greengravity/Datakey/core/coreprocessor.X/assets/assets.c

#include "assets.h"

// Systemfont: 16 pixels high
const uint16_t bitmapdata[] = 
{
// @0" " (3 pixels wide)
//    
//    
//    
//    
//    
//    
//    
//    
//    
//    
//    
//    
//    
//    
//    
//    
0x0000,0x0000,0x0000,0x0000,0x0000,0x0000,0x0000,0x0000,0x0000,0x0000,0x0000,0x0000,0x0000,0x0000,0x0000,0x0000,0x0000,0x0000,0x0000,0x0000,0x0000,0x0000,0x0000,0x0000,0x0000,0x0000,0x0000,0x0000,0x0000,0x0000,0x0000,0x0000,0x0000,0x0000,0x0000,0x0000,0x0000,0x0000,0x0000,0x0000,0x0000,0x0000,0x0000,0x0000,0x0000,0x0000,0x0000,0x0000
// @48"!" (3 pixels wide)
//    
//    
//    
//    
//  # 
//  # 
//  # 
//  # 
//  # 
//  # 
//    
//  # 
//  # 
//    
//    
//    
,0x0000,0x0000,0x0000,0x0000,0x0000,0x0000,0x0000,0x0000,0x0000,0x0000,0x0000,0x0000,0x4208,0xe73c,0x4208,0x4208,0xe73c,0x4208,0x4208,0xe73c,0x4208,0x4208,0xe73c,0x4208,0x2104,0xdedb,0x4208,0x2104,0xce79,0x2104,0x0000,0x0000,0x0000,0x4208,0xe73c,0x4208,0x4208,0xe73c,0x4208,0x0000,0x0000,0x0000,0x0000,0x0000,0x0000,0x0000,0x0000,0x0000
// @96""" (5 pixels wide)
//      
//      
//      
//  # # 
//  # # 
//  # # 
//  # # 
//      
//      
//      
//      
//      
//      
//      
//      
//      
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
  { 90,0, 7, 122 }, // z
  { 91,0, 6, 123 }, // {
  { 92,2, 6, 124 }, // |
  { 93,0, 7, 125 }, // }
  { 94,0, 9, 126 }, // ~
  { 95,0, 7, 167 }, // §
  { 96,0, 6, 176 }, // °
  { 97,0, 6, 178 }, // ²
  { 98,0, 6, 179 }, // ³
  { 99,2, 7, 180 }, // ´
  { 100,0, 10, 196 }, // Ä
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
};

const Unicodelist unicodes[] = 
{
  { 0,0 }, // zero
  { 32,1 }, //  
  { 33,2 }, // !
  { 34,3 }, // "
  { 35,4 }, // #
  { 36,5 }, // $
  { 37,6 }, // %
  { 38,7 }, // &
  { 39,8 }, // '
  { 40,9 }, // (
  { 41,10 }, // )
  { 42,11 }, // *
  { 43,12 }, // +
  { 44,13 }, // ,
  { 45,14 }, // -
  { 46,15 }, // .
  { 47,16 }, // /
  { 48,17 }, // 0
  { 49,18 }, // 1
  { 50,19 }, // 2
  { 51,20 }, // 3
  { 52,21 }, // 4
  { 53,22 }, // 5
  { 54,23 }, // 6
  { 55,24 }, // 7
  { 56,25 }, // 8
  { 57,26 }, // 9
  { 58,27 }, // :
  { 59,28 }, // ;
  { 60,29 }, // <
  { 61,30 }, // =
  { 62,31 }, // >
  { 63,32 }, // ?
  { 64,33 }, // @
  { 65,34 }, // A
  { 66,35 }, // B
  { 67,36 }, // C
  { 68,37 }, // D
  { 69,38 }, // E
  { 70,39 }, // F
  { 71,40 }, // G
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
  { 92,61 }, // Backslash
  { 93,62 }, // ]
  { 94,63 }, // ^
  { 95,64 }, // _
  { 96,65 }, // `
  { 97,66 }, // a
  { 98,67 }, // b
  { 99,68 }, // c
  { 100,69 }, // d
  { 101,70 }, // e
  { 102,71 }, // f
  { 103,72 }, // g
  { 104,73 }, // h
  { 105,74 }, // i
  { 106,75 }, // j
  { 107,76 }, // k
  { 108,77 }, // l
  { 109,78 }, // m
  { 110,79 }, // n
  { 111,80 }, // o
  { 112,81 }, // p
  { 113,82 }, // q
  { 114,83 }, // r
  { 115,84 }, // s
  { 116,85 }, // t
  { 117,86 }, // u
  { 118,87 }, // v
  { 119,88 }, // w
  { 120,89 }, // x
  { 121,90 }, // y
  { 122,91 }, // z
  { 123,92 }, // {
  { 124,93 }, // |
  { 125,94 }, // }
  { 126,95 }, // ~
  { 167,96 }, // §
  { 176,97 }, // °
  { 178,98 }, // ²
  { 179,99 }, // ³
  { 180,100 }, // ´
  { 196,101 }, // Ä
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
};

const Keyboardmaps keymaps[] = 
{
  { false, { 0x00, 0x00, 0x00, 0x00, 0x00 }, 0 }, // empty
  { false, { 0x00, 0x00, 0x00, 0x00, 0x00 }, 0 }, // empty
  { false, { 0x00, 0x00, 0x00, 0x00, 0x00 }, 0 }, // empty
  { false, { 0x00, 0x00, 0x00, 0x00, 0x00 }, 0 }, // empty
  { false, { 0x00, 0x00, 0x00, 0x00, 0x00 }, 0 }, // empty
  { false, { 0x00, 0x00, 0x00, 0x00, 0x00 }, 0 }, // empty
  { false, { 0x00, 0x00, 0x00, 0x00, 0x00 }, 0 }, // empty
  { false, { 0x00, 0x00, 0x00, 0x00, 0x00 }, 0 }, // empty
  { false, { 0x00, 0x00, 0x00, 0x00, 0x00 }, 0 }, // empty
  { false, { 0x00, 0x00, 0x00, 0x00, 0x00 }, 0 }, // empty
  { false, { 0x00, 0x00, 0x00, 0x00, 0x00 }, 0 }, // empty
  { true,  { 0x22, 0x0e, 0x3b, 0x00, 0x00 }, 0 }, // A-Z
  { true,  { 0x2e, 0x46, 0x4f, 0x56, 0x00 }, 40 }, // Menu
  { true,  { 0x42, 0x0e, 0x5b, 0x00, 0x00 }, 80 }, // a-z
  { false, { 0x00, 0x00, 0x00, 0x00, 0x00 }, 0 }, // empty
  { false, { 0x00, 0x00, 0x00, 0x00, 0x00 }, 0 }, // empty
  { false, { 0x00, 0x00, 0x00, 0x00, 0x00 }, 0 }, // empty
  { true,  { 0x02, 0x0e, 0x6b, 0x00, 0x00 }, 120 }, // !-ü
  { false, { 0x00, 0x00, 0x00, 0x00, 0x00 }, 0 }, // empty
  { false, { 0x00, 0x00, 0x00, 0x00, 0x00 }, 0 }, // empty
  { false, { 0x00, 0x00, 0x00, 0x00, 0x00 }, 0 }, // empty
  { false, { 0x00, 0x00, 0x00, 0x00, 0x00 }, 0 }, // empty
  { false, { 0x00, 0x00, 0x00, 0x00, 0x00 }, 0 }, // empty
  { false, { 0x00, 0x00, 0x00, 0x00, 0x00 }, 0 }, // empty
  { false, { 0x00, 0x00, 0x00, 0x00, 0x00 }, 0 } // empty
};
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
