greengravity/Datakey/core/coreprocessor.X/assets/assets_english_en-US.c

#include	"../assets.h"

#if ASSETPACK == ASSETPACK_english_en_US

// Systemfont: 15 pixels high
const __prog__ uint8_t __attribute__((space(prog))) bitmapdata[] = 
{
// @0" " (3 pixels wide)
//    
//    
//    
//    
//    
//    
//    
//    
//    
//    
//    
//    
//    
//    
//    
0x00,0x02,0x2d,0x00
// @4"!" (3 pixels wide)
//    
//    
//    
//  # 
//  # 
//  # 
//  # 
//  # 
//  # 
//  # 
//    
//  # 
//    
//    
//    
,0x00,0x20,0x09,0x00,0x95,0x43,0xe7,0x43,0x43,0xe7,0x43,0x43,0xe7,0x43,0x22,0xce,0x22,0x22,0xce,0x22,0x22,0xce,0x22,0x22,0xce,0x22,0x03,0x00,0x83,0x43,0xe7,0x43,0x09,0x00
// @38""" (5 pixels wide)
//      
//      
//  # # 
//  # # 
//  # # 
//      
//      
//      
//      
//      
//      
//      
//      
//      
//      
,0x00,0x14,0x0a,0x00,0x8f,0x43,0xda,0x44,0xe6,0x5e,0x43,0xc2,0x26,0xc2,0x43,0x22,0xb5,0x26,0xc2,0x43,0x32,0x00
// @60"#" (9 pixels wide)
//          
//          
//          
//       #  
//       #  
//   ###### 
//    #     
//          
//  ######  
//   #  #   
//   #      
//   #      
//          
//          
//          
,0x00,0x48,0x1e,0x00,0x85,0x43,0x80,0x00,0xa7,0x43,0x04,0x00,0x88,0x8c,0x5e,0x13,0x9c,0x13,0x00,0x00,0x8c,0x05,0xff,0x89,0xf3,0x43,0x00,0x00,0x13,0x9c,0x13,0x5e,0x8c,0x04,0x00,0x89,0x43,0x80,0x00,0x80,0x43,0x00,0x00,0x43,0xf3,0x05,0xff,0x81,0x8c,0x03,0x00,0x84,0xa7,0x43,0x43,0xa7,0x04,0x00,0x85,0x13,0x9c,0x13,0x5e,0x8c,0x04,0x00,0x85,0x43,0xa7,0x00,0x80,0x43,0x1e,0x00
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
//                
//                
//                
//                
//                
//    #           
//    #           
//    #           
//                
//                
//                
//                
//                
//                
//
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
