greengravity/Datakey/core/coreprocessor.X/assets/assets_english_en-US.h

#if ASSETPACK == ASSETPACK_english_en_US

#define MAX_IMAGE_BUFFER 225
#define TOTAL_IMAGE_COUNT 195
#define TOTAL_CHAR_COUNT 146
#define CHAR_HEIGHT 15
#define CHAR_EOL 0x00
#define CHAR_LINEFEED 0x01
#define CHAR_ENCODEERR 0x02
#define CHAR_SPACE 0x03

// bmpsize: 21394Bytes

#define KEYCOMMAND_EMPTY 0
#define KEYCOMMAND_CHAR 1
#define KEYCOMMAND_SPACE 2
#define KEYCOMMAND_BACKSPACE 3
#define KEYCOMMAND_LF 4
#define KEYCOMMAND_OK 5
#define KEYCOMMAND_ABORT 6
#define KEYCOMMAND_GEN 7

#define SYSICON_EMPTY 143
#define SYSICON_SPACETEXT 144
#define SYSICON_ENCODEERR 145
#define SYSICON_BACKSPACE 146
#define SYSICON_SPACE 147
#define SYSICON_ENTER 148
#define SYSICON_OK 149
#define SYSICON_DELETE 150
#define SYSICON_ABORT 151
#define SYSICON_ARROWUP 152
#define SYSICON_ARROWDOWN 153
#define SYSICON_SEARCH 154
#define SYSICON_SEARCHNEXT 155
#define SYSICON_SLASH 156
#define SYSICON_BRIGHTNESS 157
#define SYSICON_USB 158
#define SYSICON_COLOR 159
#define SYSICON_CLOCK 160
#define SYSICON_CALENDAR 161
#define SYSICON_COLON 162
#define SYSICON_DOT 163
#define SYSICON_SPEED 164
#define SYSICON_CHARGE 165
#define SYSICON_NOCHARGE 166
#define SYSICON_CHARGING 167
#define SYSICON_CHARGED 168
#define SYSICON_PIN_MARKER 169
#define SYSICON_PIN_GROUND 170
#define SYSICON_PIN_OBS1 171
#define SYSICON_PIN_OBS2 172
#define SYSICON_PIN_OBS3 173
#define SYSICON_PIN_OBS4 174
#define SYSICON_PIN_OBS5 175
#define SYSICON_PIN_OBS6 176
#define SYSICON_PIN_OBS7 177
#define SYSICON_PIN_OBS8 178
#define SYSICON_PIN_OBS9 179
#define SYSICON_TETRIS_BG 180
#define SYSICON_TETRIS_WALL 181
#define SYSICON_TETRIS_I 182
#define SYSICON_TETRIS_J 183
#define SYSICON_TETRIS_L 184
#define SYSICON_TETRIS_O 185
#define SYSICON_TETRIS_S 186
#define SYSICON_TETRIS_T 187
#define SYSICON_TETRIS_Z 188
#define SYSICON_BUTTON_A 189
#define SYSICON_BUTTON_B 190
#define SYSICON_BUTTON_LEFT 191
#define SYSICON_BUTTON_RIGHT 192
#define SYSICON_BUTTON_UP 193
#define SYSICON_BUTTON_DOWN 194

#define TEXT_EMPTY 0
#define TEXT_ERROR_CONTEXT 1
#define TEXT_ERROR_SD_CD 2
#define TEXT_ERROR_SD_FAILURE 3
#define TEXT_TEST 4
#define TEXT_ENTER_NEW_KEY 5
#define TEXT_ENTER_VERIFY_KEY 6
#define TEXT_ENTER_CHECK_KEY 7
#define TEXT_ENTER_KEY_ERROR 8
#define TEXT_ENTER_NEW_KEY_ERROR 9
#define TEXT_ENTER_SEARCHFIELD 10
#define TEXT_SEARCH_NO_ENTRIES 11
#define TEXT_SEARCH_LAST_ENTRY 12
#define TEXT_IOHEAD_NEW 13
#define TEXT_IOHEAD_NAME 14
#define TEXT_IOHEAD_USER 15
#define TEXT_IOHEAD_URL 16
#define TEXT_IOHEAD_KEY 17
#define TEXT_IOHEAD_KEY2 18
#define TEXT_IOHEAD_INFO 19
#define TEXT_VIEWHEAD_NAME 20
#define TEXT_VIEWHEAD_USER 21
#define TEXT_VIEWHEAD_URL 22
#define TEXT_VIEWHEAD_KEY 23
#define TEXT_VIEWHEAD_KEY2 24
#define TEXT_VIEWHEAD_INFO 25
#define TEXT_TKNAME_NAME 26
#define TEXT_TKNAME_USER 27
#define TEXT_TKNAME_KEY1 28
#define TEXT_TKNAME_KEY2 29
#define TEXT_TKNAME_URL 30
#define TEXT_TKNAME_INFO 31
#define TEXT_HEAD_ENTRY_DETAIL 32
#define TEXT_HEAD_ENTRY_OVERVIEW 33
#define TEXT_HEAD_OPTIONS 34
#define TEXT_HEAD_PINOPTIONS 35
#define TEXT_OPTV_USB_OFF 36
#define TEXT_OPTV_USB_KEYBOARD 37
#define TEXT_OPTV_QKEYS_OFF 38
#define TEXT_OPTV_QKEYS_ON 39
#define TEXT_MSG_OVERWRITE 40
#define TEXT_MSG_DELETE_TOKEN 41
#define TEXT_MSG_DELETE_ENTRY 42
#define TEXT_MSG_ABORT 43
#define TEXT_CHB_SEARCH_ENTRY 44
#define TEXT_CHB_CREATE_ENTRY 45
#define TEXT_CHB_DELETE_ENTRY 46
#define TEXT_CHB_OPTIONS 47
#define TEXT_CHB_DEVICEOPTIONS 48
#define TEXT_CHB_PINOPTIONS 49
#define TEXT_CHB_GAMES 50
#define TEXT_CHB_RETURN_OVERVIEW 51
#define TEXT_CHB_EDIT_TOKEN 52
#define TEXT_CHB_DELETE_TOKEN 53
#define TEXT_CHB_PUSH_TOKEN 54
#define TEXT_WRITE_USB_OUT 55
#define TEXT_PIN_INF_LEVEL 56
#define TEXT_PIN_INF_LEVELNR 57
#define TEXT_PIN_INF_STEPS 58
#define TEXT_PIN_INF_LIVES 59
#define TEXT_PIN_INF_NO_STEPS 60
#define TEXT_PIN_INF_SPLIT_STEPS 61
#define TEXT_PIN_INF_GE_ENTER_PIN 62
#define TEXT_PIN_INF_GE_VERIFY_PIN 63
#define TEXT_PIN_INF_GE_PIN_ERROR 64
#define TEXT_OPT_CHANGE_PIN 65
#define TEXT_OPT_PIN_TRIES 66
#define TEXT_OPT_PIN_LEN 67
#define TEXT_OPTINF_PIN_LEN_CHANGED 68
#define TEXT_TETRIS_GAME_OVER1 69
#define TEXT_TETRIS_GAME_OVER2 70
#define TEXT_TETRIS_GAME_START1 71
#define TEXT_TETRIS_GAME_START2 72
#define TEXT_TETRIS_SCORE 73
#define TEXT_TETRIS_LINES 74
#define TEXT_TETRIS_LEVEL 75

#define DEFAULT_KEYMAP 3

#define PASSWORD_REPLACE_CHAR 0x0d

#endif
