greengravity/Datakey/core/coreprocessor.X/assets/assets_english_en-GB.h

#if ASSETPACK == ASSETPACK_english_en_GB

#define MAX_IMAGE_BUFFER 225
#define TOTAL_IMAGE_COUNT 150
#define TOTAL_CHAR_COUNT 107
#define CHAR_HEIGHT 15
#define CHAR_EOL 0x00
#define CHAR_LINEFEED 0x01
#define CHAR_ENCODEERR 0x02
#define CHAR_SPACE 0x03

// bmpsize: 17165Bytes

#define KEYCOMMAND_EMPTY 0
#define KEYCOMMAND_CHAR 1
#define KEYCOMMAND_SPACE 2
#define KEYCOMMAND_BACKSPACE 3
#define KEYCOMMAND_LF 4
#define KEYCOMMAND_OK 5
#define KEYCOMMAND_ABORT 6
#define KEYCOMMAND_GEN 7

#define SYSICON_EMPTY 104
#define SYSICON_SPACETEXT 105
#define SYSICON_ENCODEERR 106
#define SYSICON_BACKSPACE 107
#define SYSICON_SPACE 108
#define SYSICON_ENTER 109
#define SYSICON_OK 110
#define SYSICON_DELETE 111
#define SYSICON_ABORT 112
#define SYSICON_ARROWUP 113
#define SYSICON_ARROWDOWN 114
#define SYSICON_SEARCH 115
#define SYSICON_SEARCHNEXT 116
#define SYSICON_SLASH 117
#define SYSICON_BRIGHTNESS 118
#define SYSICON_USB 119
#define SYSICON_COLOR 120
#define SYSICON_CLOCK 121
#define SYSICON_CALENDAR 122
#define SYSICON_COLON 123
#define SYSICON_DOT 124
#define SYSICON_SPEED 125
#define SYSICON_CHARGE 126
#define SYSICON_NOCHARGE 127
#define SYSICON_CHARGING 128
#define SYSICON_CHARGED 129
#define SYSICON_PIN_MARKER 130
#define SYSICON_PIN_GROUND 131
#define SYSICON_PIN_OBS1 132
#define SYSICON_PIN_OBS2 133
#define SYSICON_PIN_OBS3 134
#define SYSICON_PIN_OBS4 135
#define SYSICON_PIN_OBS5 136
#define SYSICON_PIN_OBS6 137
#define SYSICON_PIN_OBS7 138
#define SYSICON_PIN_OBS8 139
#define SYSICON_PIN_OBS9 140
#define SYSICON_TETRIS_BG 141
#define SYSICON_TETRIS_WALL 142
#define SYSICON_TETRIS_I 143
#define SYSICON_TETRIS_J 144
#define SYSICON_TETRIS_L 145
#define SYSICON_TETRIS_O 146
#define SYSICON_TETRIS_S 147
#define SYSICON_TETRIS_T 148
#define SYSICON_TETRIS_Z 149

#define TEXT_EMPTY 0
#define TEXT_ERROR_CONTEXT 1
#define TEXT_ERROR_SD_CD 2
#define TEXT_ERROR_SD_FAILURE 3
#define TEXT_TEST 4
#define TEXT_ENTER_NEW_KEY 5
#define TEXT_ENTER_NEW_KEY_ERROR 6
#define TEXT_ENTER_SEARCHFIELD 7
#define TEXT_SEARCH_NO_ENTRIES 8
#define TEXT_SEARCH_LAST_ENTRY 9
#define TEXT_IOHEAD_NEW 10
#define TEXT_IOHEAD_NAME 11
#define TEXT_IOHEAD_USER 12
#define TEXT_IOHEAD_URL 13
#define TEXT_IOHEAD_KEY 14
#define TEXT_IOHEAD_KEY2 15
#define TEXT_IOHEAD_INFO 16
#define TEXT_VIEWHEAD_NAME 17
#define TEXT_VIEWHEAD_USER 18
#define TEXT_VIEWHEAD_URL 19
#define TEXT_VIEWHEAD_KEY 20
#define TEXT_VIEWHEAD_KEY2 21
#define TEXT_VIEWHEAD_INFO 22
#define TEXT_TKNAME_NAME 23
#define TEXT_TKNAME_USER 24
#define TEXT_TKNAME_KEY1 25
#define TEXT_TKNAME_KEY2 26
#define TEXT_TKNAME_URL 27
#define TEXT_TKNAME_INFO 28
#define TEXT_HEAD_ENTRY_DETAIL 29
#define TEXT_HEAD_ENTRY_OVERVIEW 30
#define TEXT_HEAD_OPTIONS 31
#define TEXT_HEAD_PINOPTIONS 32
#define TEXT_OPTV_USB_OFF 33
#define TEXT_OPTV_USB_KEYBOARD 34
#define TEXT_OPTV_QKEYS_OFF 35
#define TEXT_OPTV_QKEYS_ON 36
#define TEXT_MSG_OVERWRITE 37
#define TEXT_MSG_DELETE_TOKEN 38
#define TEXT_MSG_DELETE_ENTRY 39
#define TEXT_MSG_ABORT 40
#define TEXT_CHB_SEARCH_ENTRY 41
#define TEXT_CHB_CREATE_ENTRY 42
#define TEXT_CHB_DELETE_ENTRY 43
#define TEXT_CHB_OPTIONS 44
#define TEXT_CHB_DEVICEOPTIONS 45
#define TEXT_CHB_PINOPTIONS 46
#define TEXT_CHB_GAMES 47
#define TEXT_CHB_RETURN_OVERVIEW 48
#define TEXT_CHB_EDIT_TOKEN 49
#define TEXT_CHB_DELETE_TOKEN 50
#define TEXT_CHB_PUSH_TOKEN 51
#define TEXT_WRITE_USB_OUT 52
#define TEXT_PIN_INF_LEVEL 53
#define TEXT_PIN_INF_LEVELNR 54
#define TEXT_PIN_INF_STEPS 55
#define TEXT_PIN_INF_LIVES 56
#define TEXT_PIN_INF_NO_STEPS 57
#define TEXT_PIN_INF_SPLIT_STEPS 58
#define TEXT_PIN_INF_GE_ENTER_PIN 59
#define TEXT_PIN_INF_GE_VERIFY_PIN 60
#define TEXT_PIN_INF_GE_PIN_ERROR 61
#define TEXT_OPT_CHANGE_PIN 62
#define TEXT_OPT_PIN_TRIES 63
#define TEXT_OPT_PIN_LEN 64
#define TEXT_OPTINF_PIN_LEN_CHANGED 65
#define TEXT_TETRIS_GAME_OVER1 66
#define TEXT_TETRIS_GAME_OVER2 67
#define TEXT_TETRIS_GAME_START1 68
#define TEXT_TETRIS_GAME_START2 69
#define TEXT_TETRIS_SCORE 70
#define TEXT_TETRIS_LINES 71
#define TEXT_TETRIS_LEVEL 72

#define DEFAULT_KEYMAP 3

#define PASSWORD_REPLACE_CHAR 0x0d

#endif
